jharvey/T-Deck_JH/schematic/T-Deck_Mockup_KiCad/t-deck.kicad_sch

## KiCad design schematic/T-Deck_Mockup_KiCad/t-deck.kicad_sch (2024-01-16)

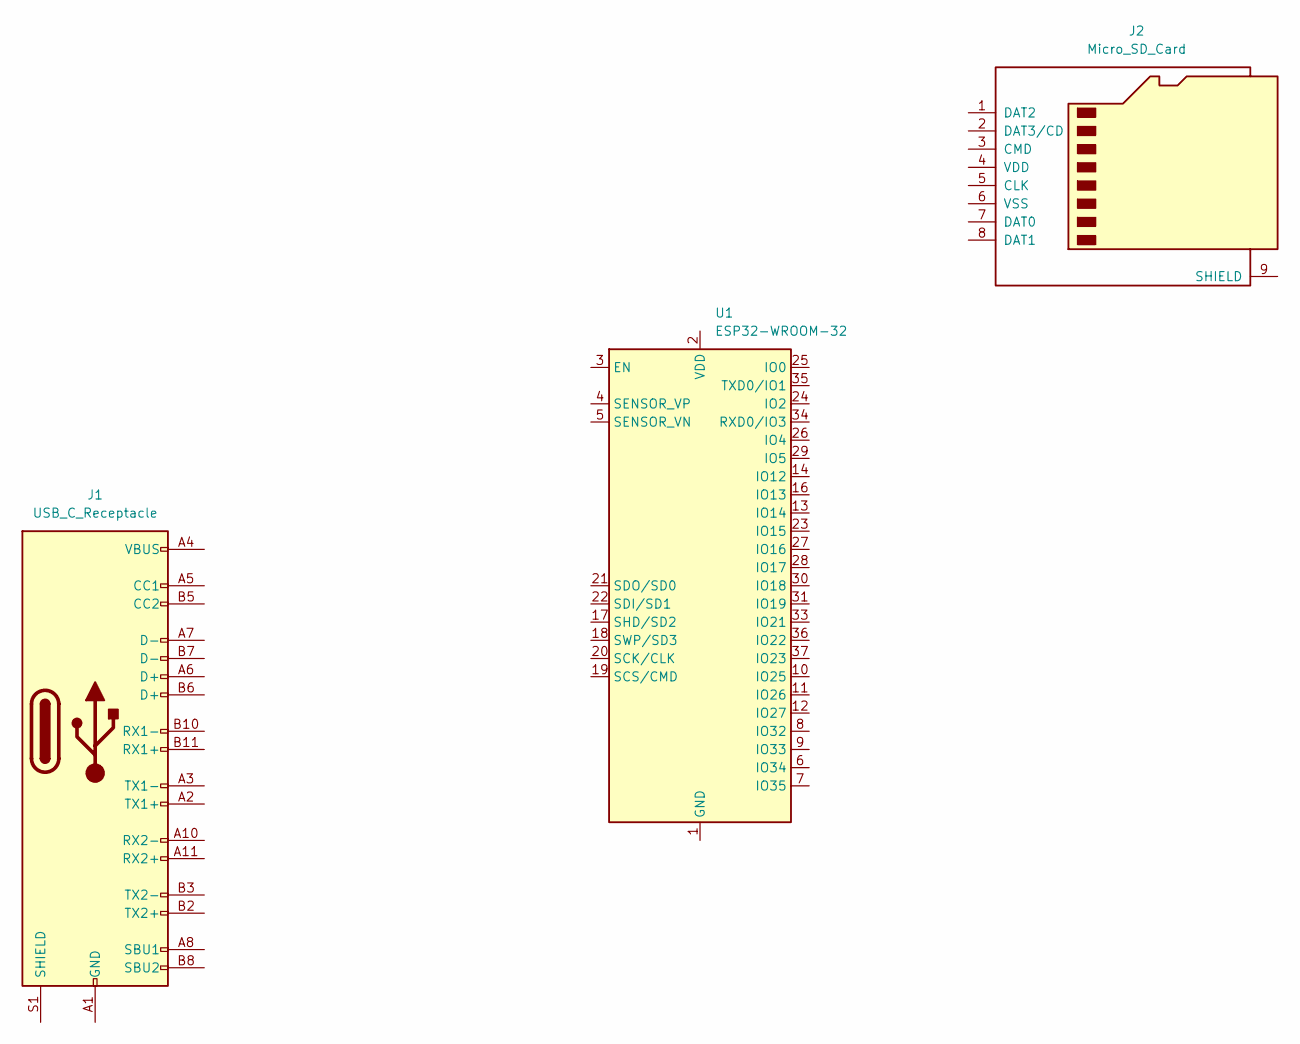
[picture p14: schematic t-deck.kicad_sch]

Parts:
J1: USB_C_Receptacle
J2: Micro_SD_Card
U1: ESP32-WROOM-32

Connections:
unnamed: J1.A1 (GND), J1.A12 (GND), J1.B1 (GND), J1.B12 (GND)
unnamed: J1.A4 (VBUS), J1.A9 (VBUS), J1.B4 (VBUS), J1.B9 (VBUS)
unnamed: U1.1 (GND), U1.15 (GND), U1.38 (GND), U1.39 (GND)
