jharvey/T-Deck_JH/schematic/Misc/USB_LIPO_Charger_Mockup_KiCad/USB_LIPO_Charger.kicad_sch

## KiCad design schematic/Misc/USB_LIPO_Charger_Mockup_KiCad/USB_LIPO_Charger.kicad_sch (2024-02-18)

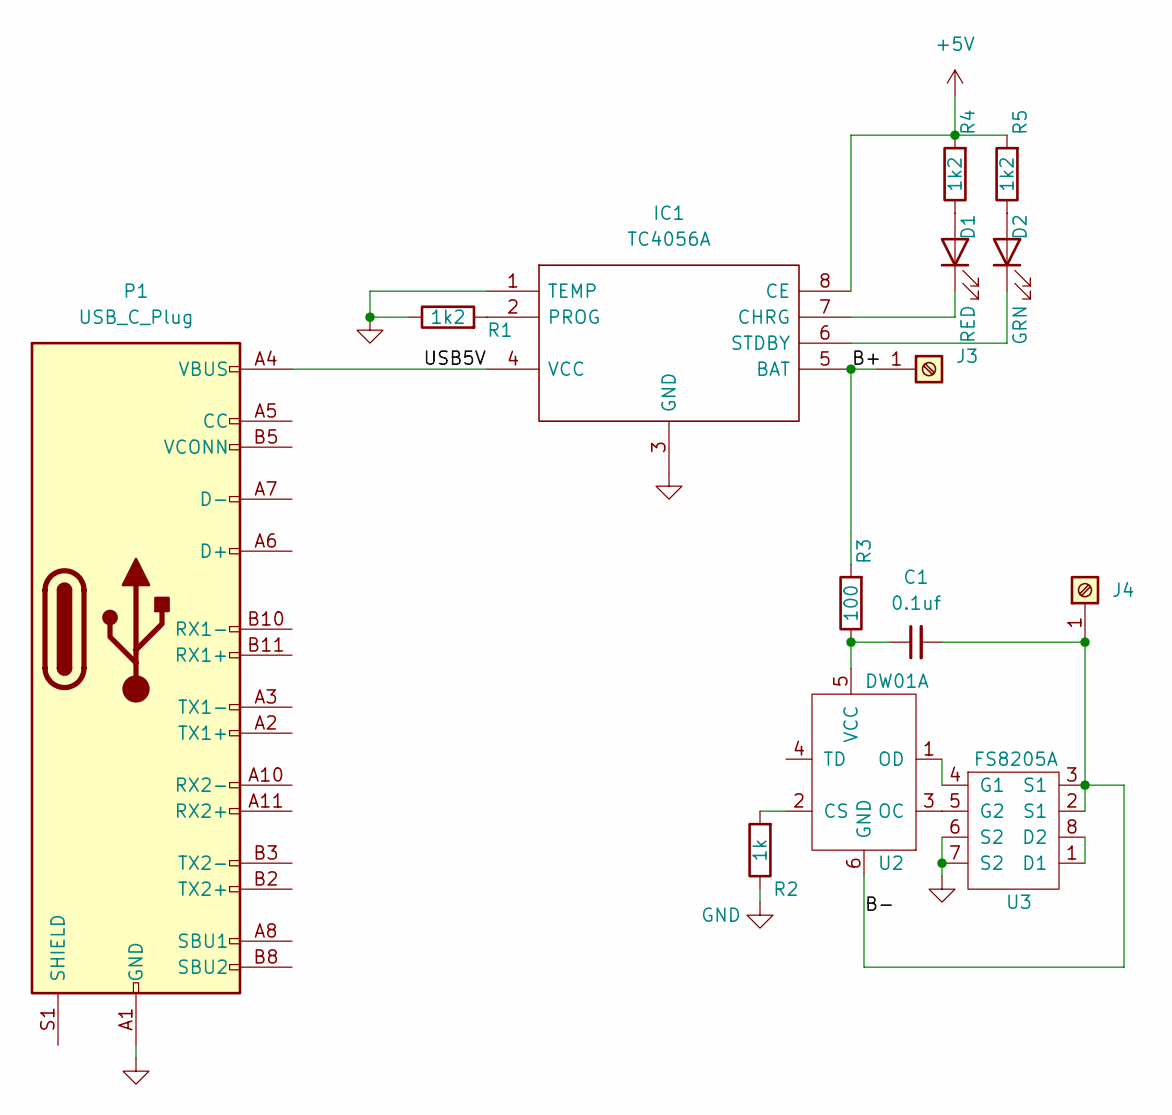
[picture p15: schematic USB_LIPO_Charger.kicad_sch]

Parts:
C1: 0.1uf; C_0201_0603Metric
D1: RED; LED_0805_2012Metric
D2: GRN; LED_0805_2012Metric
IC1: TC4056A; SOIC127P600X175-9N; Manufacturer_Part_Number TC4056A
J3, J4: Screw_Terminal_01x01
P1: USB_C_Plug
R1, R4, R5: 1k2; R_0201_0603Metric
R2: 1k; R_0201_0603Metric
R3: 100; R_0201_0603Metric
U2: DW01A; SOT-23-6
U3: FS8205A; TSSOP-8_4.4x3mm_P0.65mm

Connections:
+5V: IC1.8 (CE), R4.2, R5.2
B+: IC1.5 (BAT), J3.1, R3.2
B-: C1.2, J4.1, U2.6 (GND), U3.2 (S1), U3.3 (S1)
GND: IC1.1 (TEMP), IC1.3 (GND), P1.A1 (GND), P1.A12 (GND), P1.B1 (GND), P1.B12 (GND), R1.1, R2.1, U3.6 (S2), U3.7 (S2)
unnamed: C1.1, R3.1, U2.5 (VCC)
unnamed: D1.1 (K), IC1.7 (CHRG)
unnamed: D1.2 (A), R4.1
unnamed: D2.1 (K), IC1.6 (STDBY)
unnamed: D2.2 (A), R5.1
unnamed: IC1.2 (PROG), R1.2
unnamed: R2.2, U2.2 (CS)
unnamed: U2.1 (OD), U3.4 (G1)
unnamed: U2.3 (OC), U3.5 (G2)
unnamed: U3.1 (D1), U3.8 (D2)
USB5V: IC1.4 (VCC), P1.A4 (VBUS), P1.A9 (VBUS), P1.B4 (VBUS), P1.B9 (VBUS)
